ZhangKeLiang0627/EasyGPS/2.Firmware/src/App/Common/HAL/HAL.h

/*
 * MIT License
 * Copyright (c) 2021 _VIFEXTech
 *
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
 * THE SOFTWARE IS PROVIDED "AS IS", WITHOUT WARRANTY OF ANY KIND, EXPRESS OR
 * IMPLIED, INCLUDING BUT NOT LIMITED TO THE WARRANTIES OF MERCHANTABILITY,
 * FITNESS FOR A PARTICULAR PURPOSE AND NONINFRINGEMENT. IN NO EVENT SHALL THE
 * AUTHORS OR COPYRIGHT HOLDERS BE LIABLE FOR ANY CLAIM, DAMAGES OR OTHER
 * LIABILITY, WHETHER IN AN ACTION OF CONTRACT, TORT OR OTHERWISE, ARISING FROM,
 * OUT OF OR IN CONNECTION WITH THE SOFTWARE OR THE USE OR OTHER DEALINGS IN THE
 * SOFTWARE.
 */
#ifndef __HAL_H
#define __HAL_H

#include <stdint.h>
#include "HAL_Def.h"
#include "CommonMacro.h"

namespace HAL
{
    typedef bool (*CommitFunc_t)(void *info, void *userData);

    void HAL_Init(void);
    void HAL_Update(void);

    /* Backlight */
    void Backlight_Init();
    uint16_t Backlight_GetValue();
    void Backlight_SetValue(int16_t val);
    void Backlight_SetGradual(uint16_t target, uint16_t time = 500);
    void Backlight_ForceLit(bool en);

    /* Display */
    void Display_Init();
    void Display_DumpCrashInfo(const char *info);
    void Display_SetAddrWindow(int16_t x0, int16_t y0, int16_t x1, int16_t y1);
    void Display_SendPixels(const uint16_t *pixels, uint32_t len);

    typedef void (*Display_CallbackFunc_t)(void);
    void Display_SetSendFinishCallback(Display_CallbackFunc_t func);

    /* FaultHandle */
    void FaultHandle_Init();

    /* I2C */
    int I2C_Scan();

    /* IMU */
    void IMU_Init(void);
    void IMU_SetCommitCallback(CommitFunc_t func, void *userData);
    void IMU_Update();

    /* MAG */
    bool MAG_Init();
    void MAG_SetCommitCallback(CommitFunc_t func, void *userData);
    void MAG_Update();
    void MAG_GetInfo(MAG_Info_t *info);
    void MAG_SetCalibration(void);

    /* SD */
    bool SD_Init();
    void SD_Update();
    bool SD_GetReady();
    float SD_GetCardSizeMB();
    const char *SD_GetTypeName();
    typedef void (*SD_CallbackFunction_t)(bool insert);
    void SD_SetEventCallback(SD_CallbackFunction_t callback);

    /* Power */
    void Power_Init();
    void Power_HandleTimeUpdate();
    void Power_SetAutoLowPowerTimeout(uint16_t sec);
    uint16_t Power_GetAutoLowPowerTimeout();
    void Power_SetAutoLowPowerEnable(bool en);
    void Power_Shutdown();
    void Power_Update();
    void Power_EventMonitor();
    void Power_GetInfo(Power_Info_t *info);
    typedef void (*Power_CallbackFunction_t)(void);
    void Power_SetEventCallback(Power_CallbackFunction_t callback);

    /* Clock */
    void Clock_Init();
    void Clock_GetInfo(Clock_Info_t *info);
    void Clock_SetInfo(const Clock_Info_t *info);
    const char *Clock_GetWeekString(uint8_t week);

    /* GPS */
    void GPS_Init();
    void GPS_Update();
    bool GPS_GetInfo(GPS_Info_t *info);
    bool GPS_LocationIsValid();
    double GPS_GetDistanceOffset(GPS_Info_t *info, double preLong, double preLat);

    /* Buzzer */
    void Buzz_init();
    void Buzz_SetEnable(bool en);
    void Buzz_Tone(uint32_t freq, int32_t duration = -1);

    /* Encoder */
    void Encoder_Init();
    void Encoder_Update();
    int32_t Encoder_GetDiff();
    bool Encoder_GetIsPush();
    void Encoder_SetEnable(bool en);

    /* Audio */
    void Audio_Init();
    void Audio_Update();
    bool Audio_PlayMusic(const char *name);

    /* Memory */
    void Memory_DumpInfo();

    /* ENV */
    void ENV_Init(void);
    void ENV_SetCommitCallback(CommitFunc_t func, void *userData);
    void ENV_Update(void);

    /* WiFi */
    void WiFi_Init(void);
    void WiFi_Update(void);
    void WiFi_APSetEnable(bool en);
    void WiFi_STASetEnable(bool en);
    void WiFi_GetInfo(WiFi_Info_t *info);

    /* BLE */
    void BLE_Init(void);
    void BLE_Update(void);
    void BLE_SetBegin(void);
    void BLE_SetSleep(void);
    void BLE_GetInfo(HAL::BLE_Info_t *info);
    void BLE_SetKeyboardValue(uint8_t *c);
    void BLE_SetMouseMoveValue(uint8_t *c);
    void BLE_SetMouseClickValue(uint16_t b);

    /* SmartAssistant */
    bool SmartAssistant_Init();
    void SmartAssistant_SetBegin(bool en);
    void SmartAssistant_GetInfo(HAL::Saa_Info_t *info);
}

#endif
